is-watering/isw_oozy/firmware/qmk/evidence/evidence.jpg

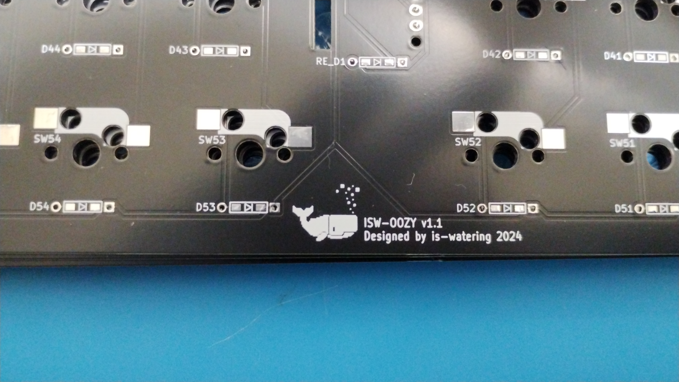
firmware/qmk/evidence/evidence.jpg
